Toolauth/wing-combo/docs/img/map/location-5v-power.png

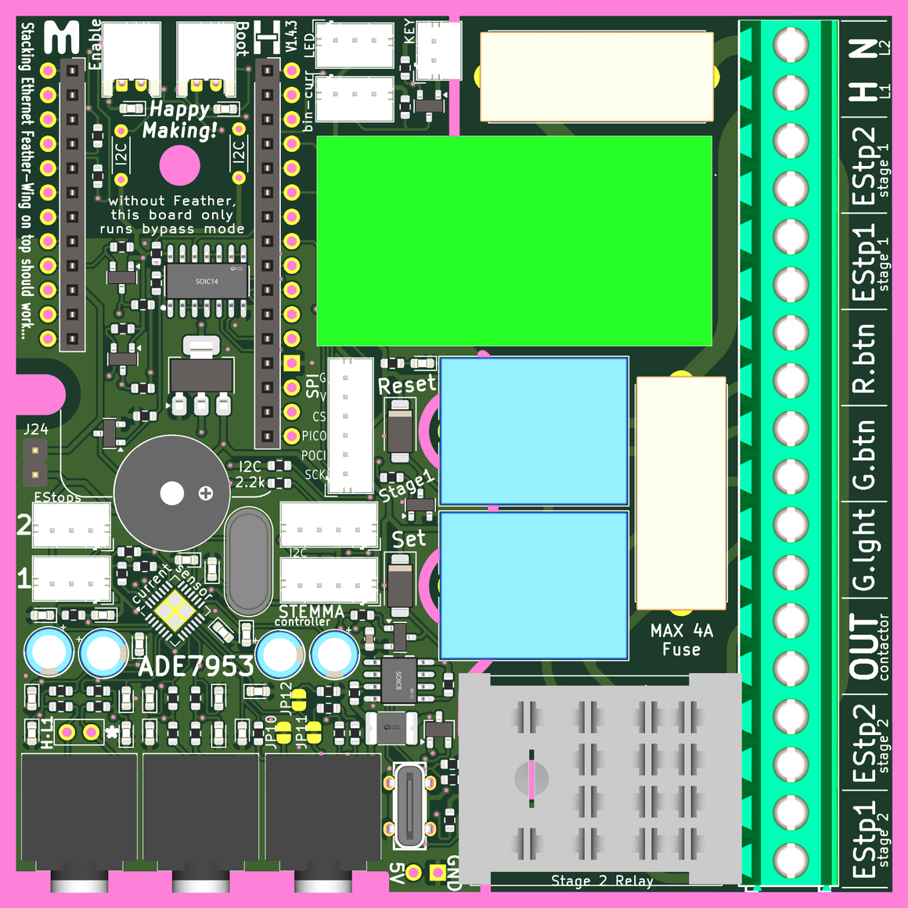
docs/img/map/location-5v-power.png
