Toolauth/wing-combo/docs/img/map/location-contactor.png

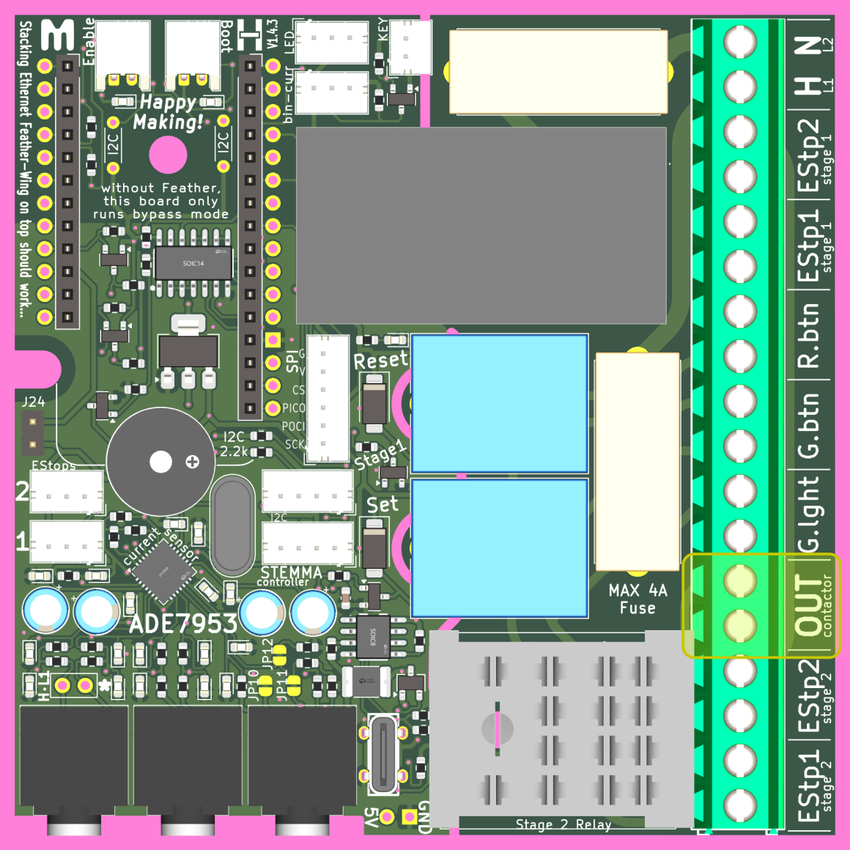
docs/img/map/location-contactor.png
