Toolauth/wing-combo/docs/img/map/location-current-a.png

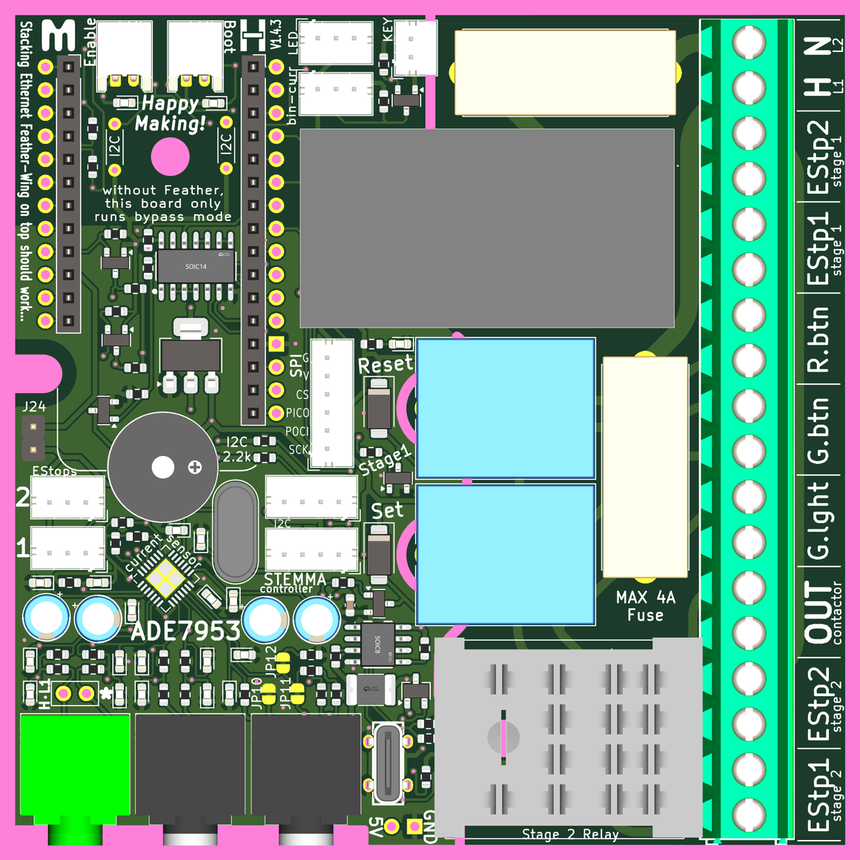
docs/img/map/location-current-a.png
