Toolauth/wing-combo/docs/img/map/location-current-b.png

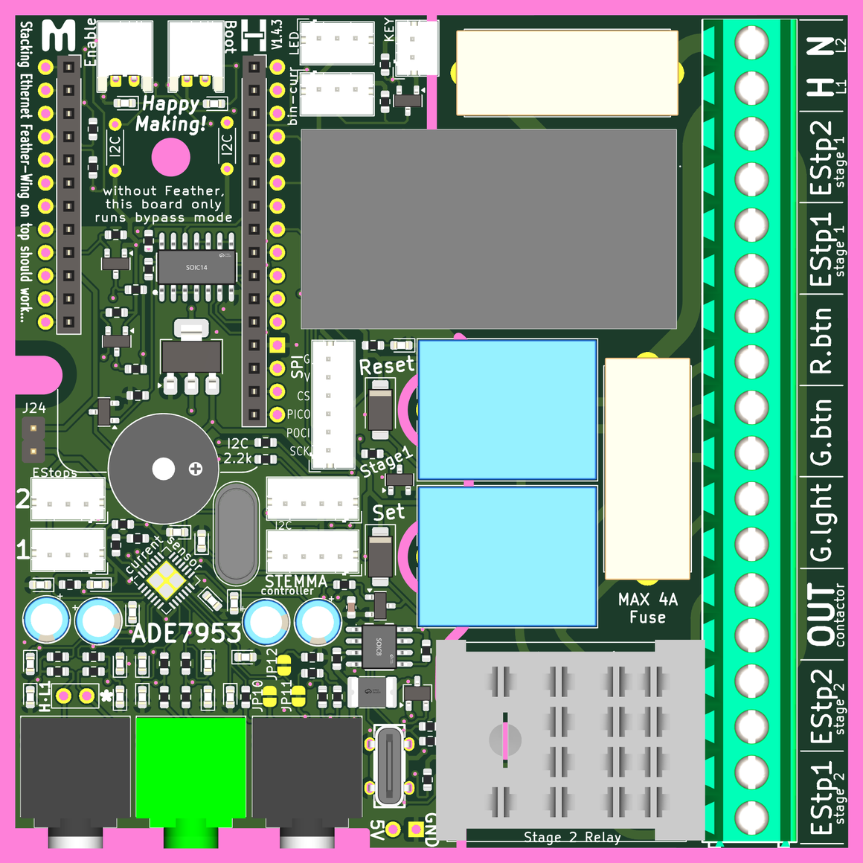
docs/img/map/location-current-b.png
