Toolauth/wing-combo/docs/img/map/location-feather-seat.png

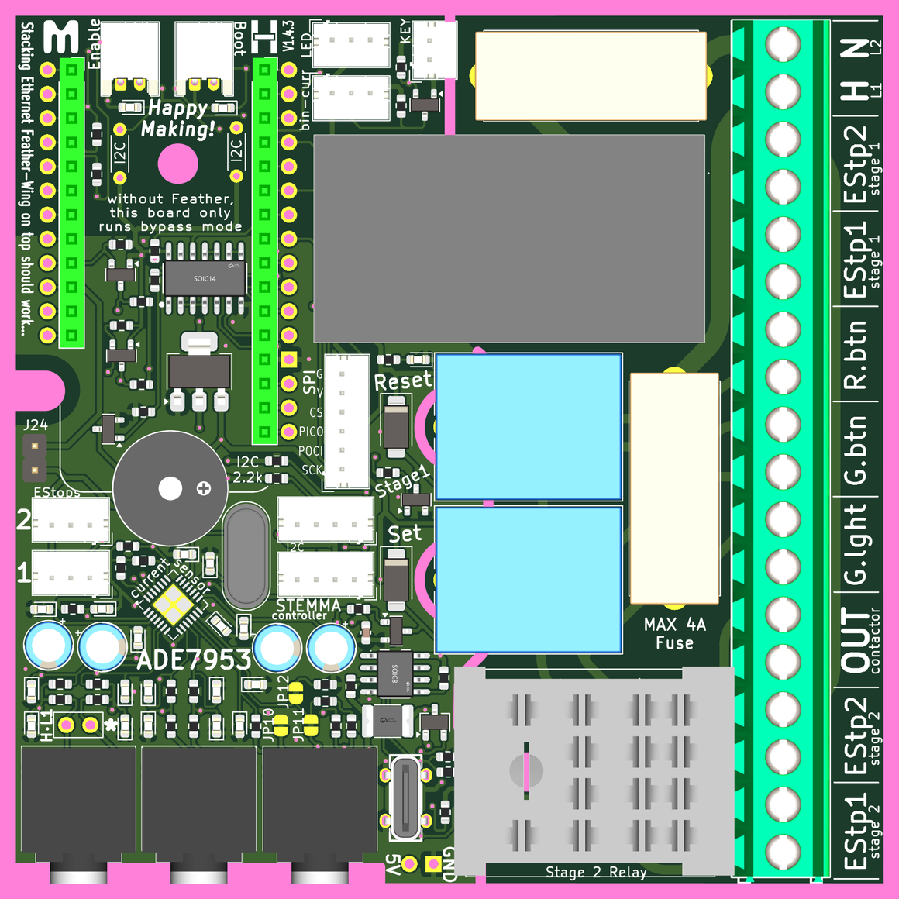
docs/img/map/location-feather-seat.png
