Toolauth/wing-combo/docs/img/map/location-fuses.png

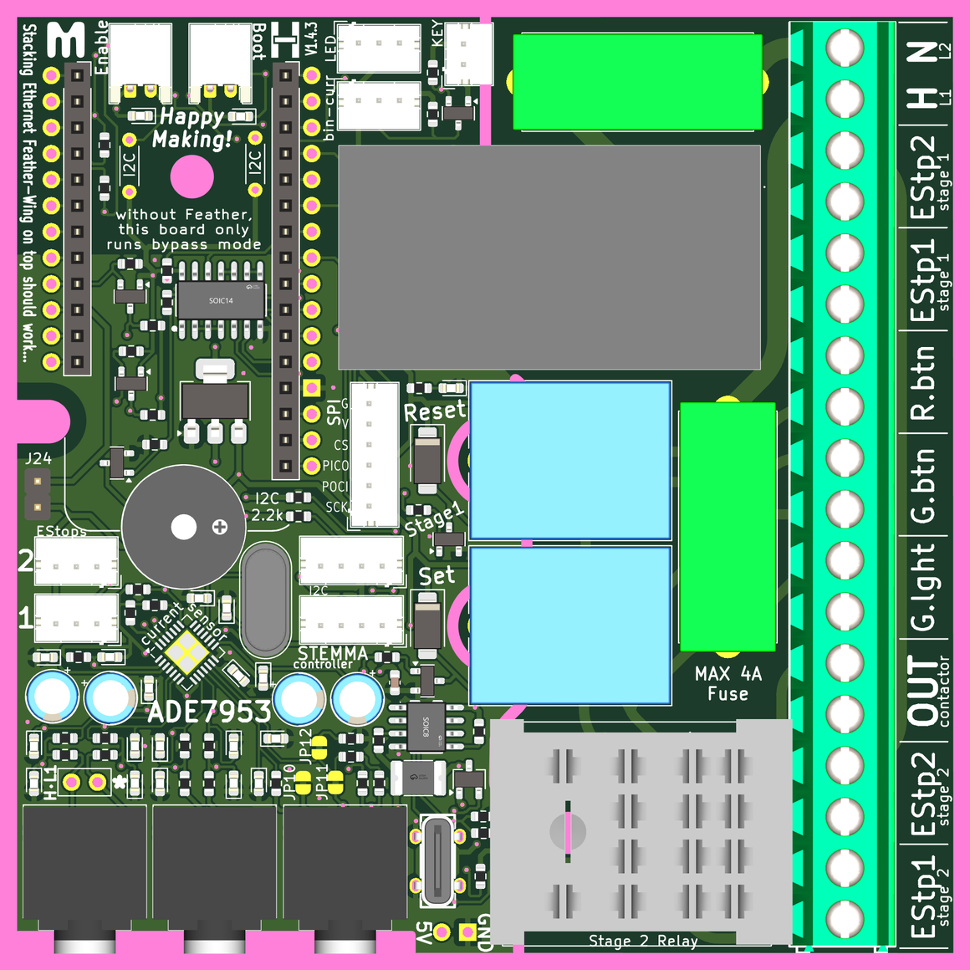
docs/img/map/location-fuses.png
