Toolauth/wing-combo/docs/img/map/location-i2c.png

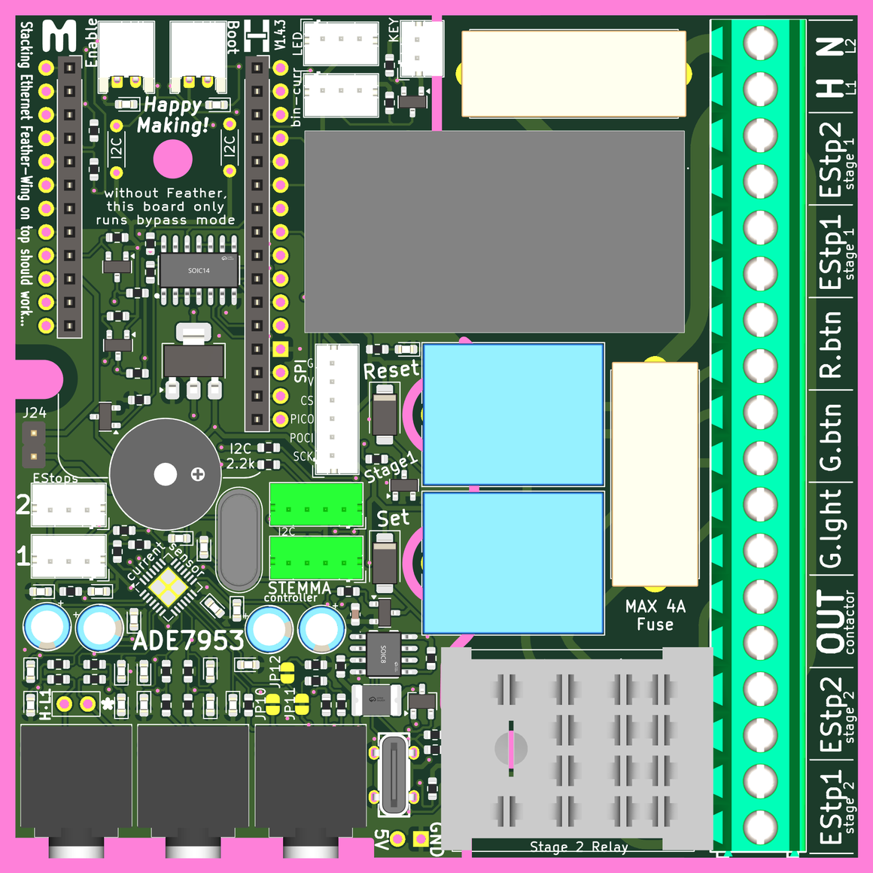
docs/img/map/location-i2c.png
