Toolauth/wing-combo/docs/img/map/location-stage-2.png

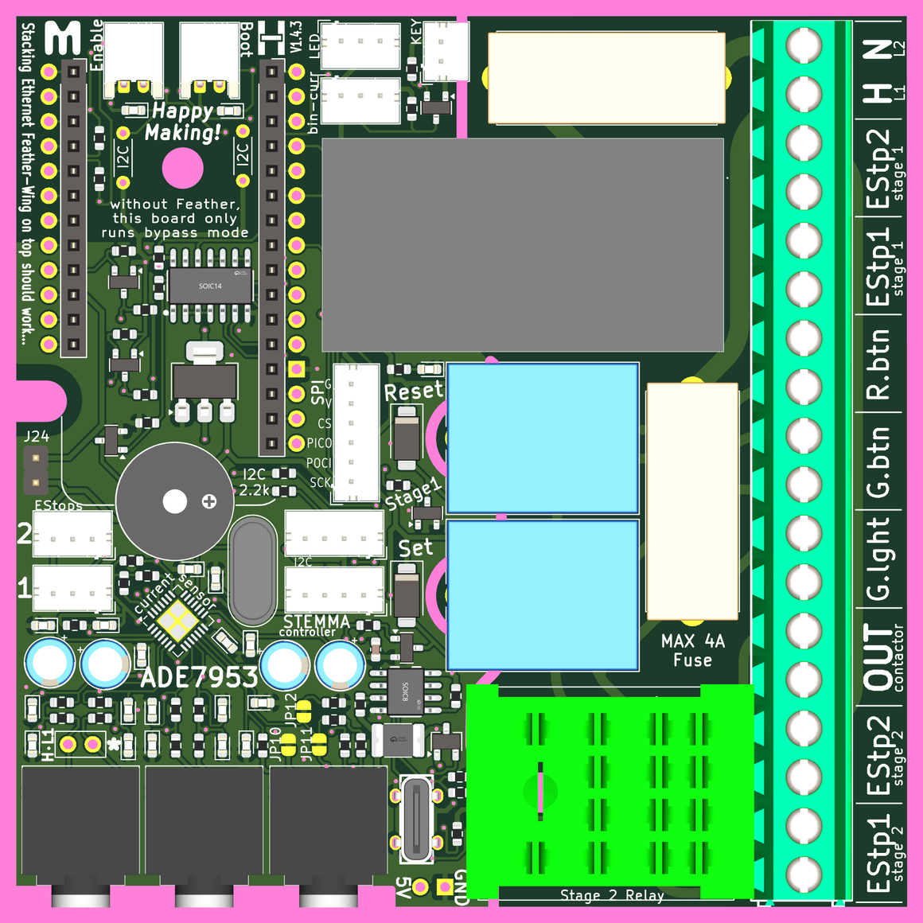
docs/img/map/location-stage-2.png
