Toolauth/wing-combo/docs/img/map/ortho-back-rt.png

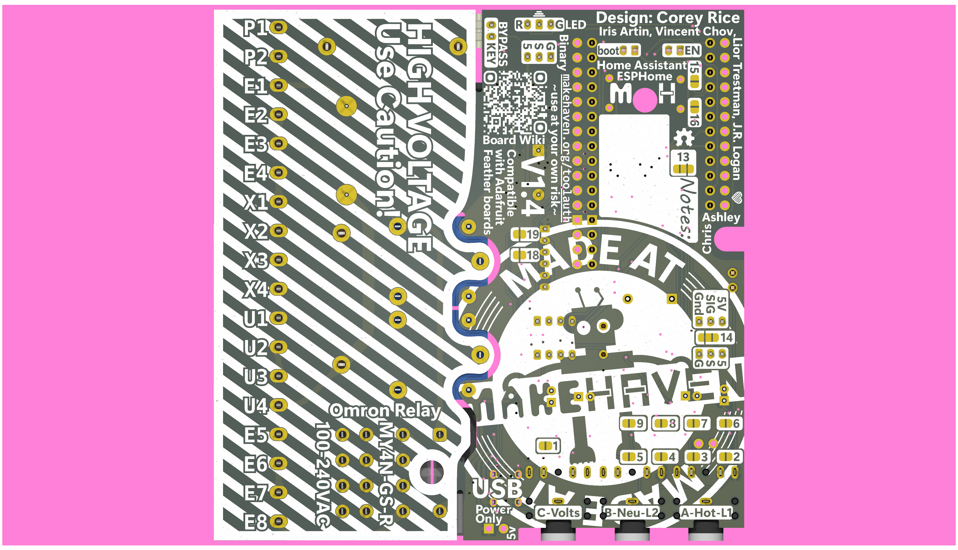
docs/img/map/ortho-back-rt.png
