Toolauth/wing-combo/docs/img/map/ortho-back.png

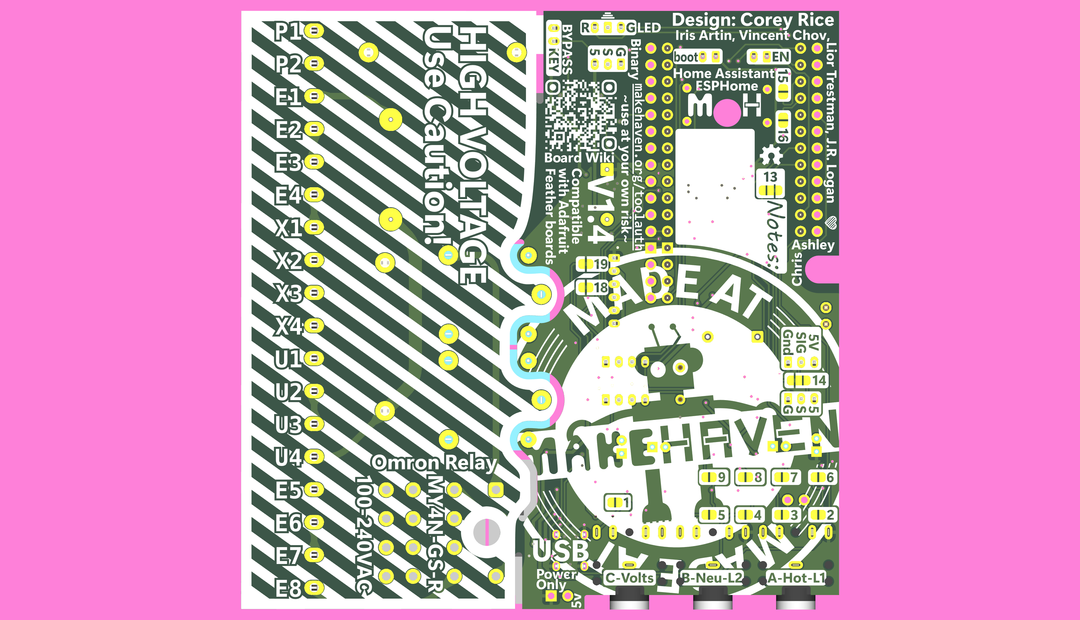
docs/img/map/ortho-back.png
