Toolauth/wing-combo/docs/img/map/ortho-front-rt.png

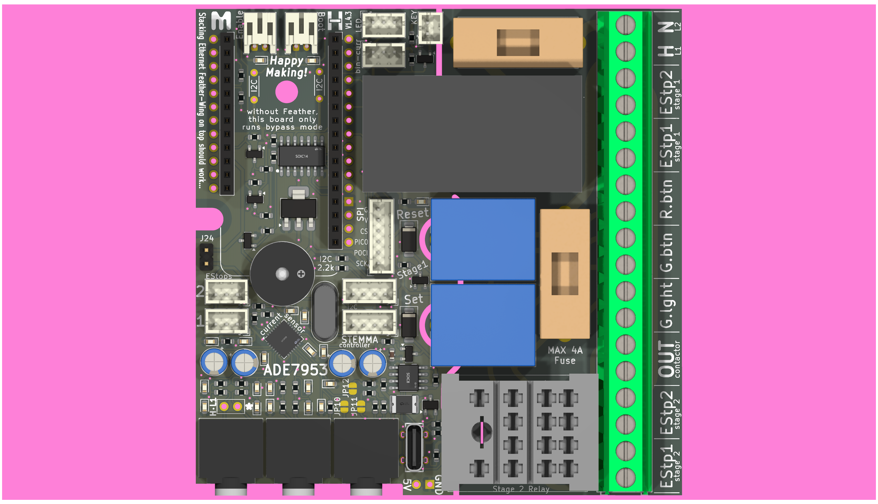
docs/img/map/ortho-front-rt.png
