Toolauth/wing-combo/docs/img/map/ortho-front.png

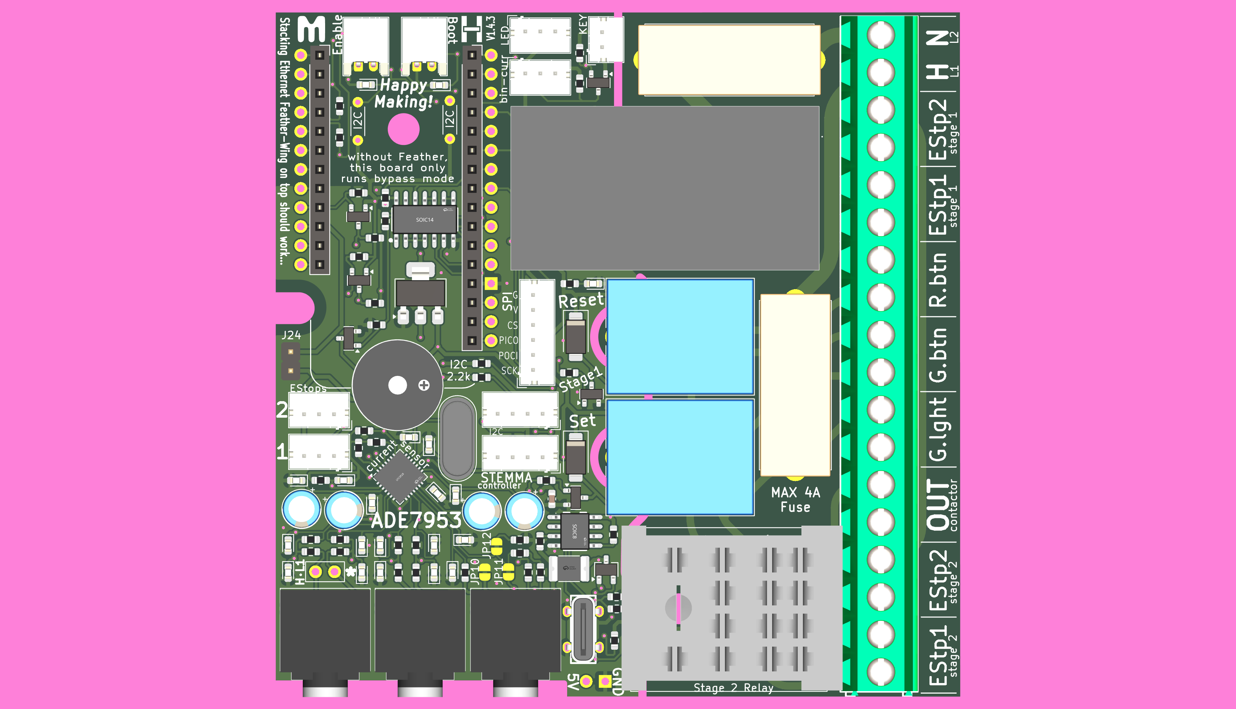
docs/img/map/ortho-front.png
