Toolauth/wing-combo/docs/img/map/sq-ortho-back.png

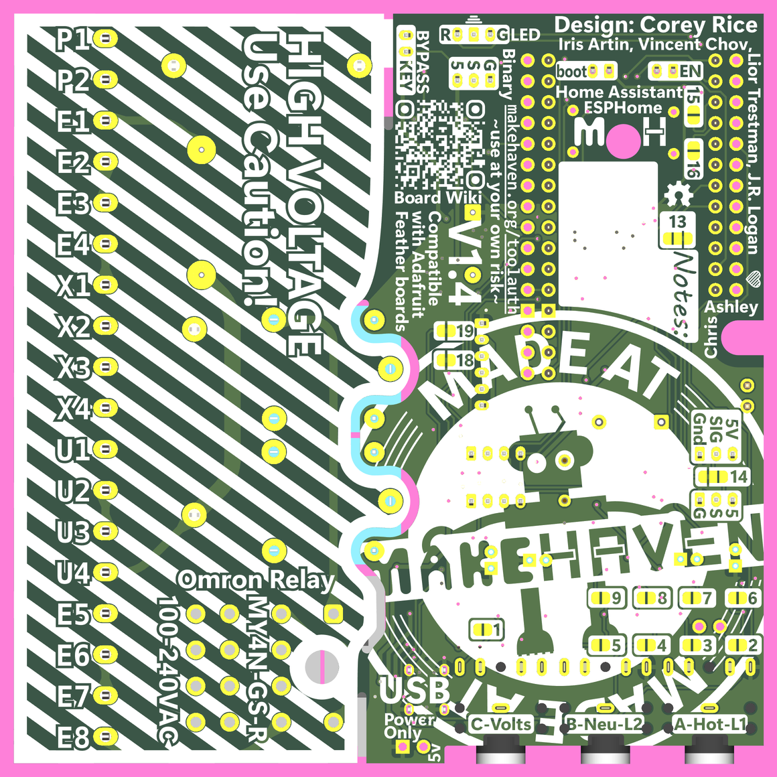
docs/img/map/sq-ortho-back.png
