Toolauth/wing-combo/docs/img/map/sq-ortho-front-rt.png

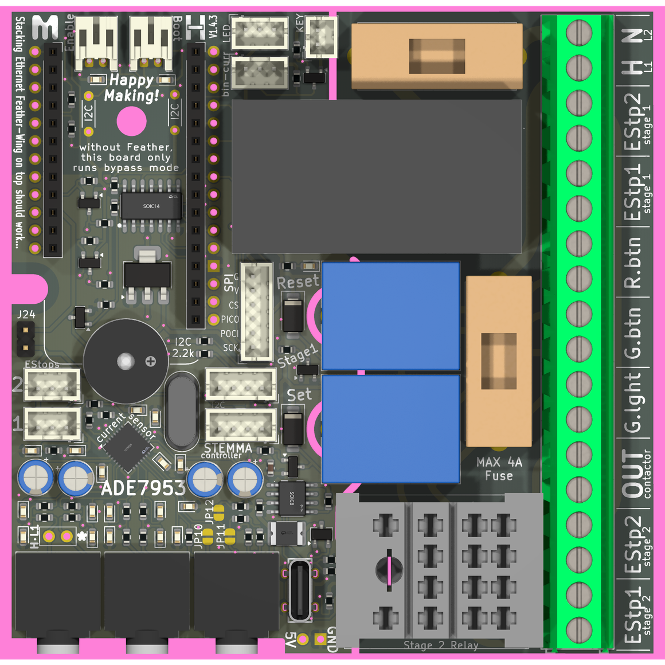
docs/img/map/sq-ortho-front-rt.png
