Toolauth/wing-combo/docs/img/offset-rt-front.png

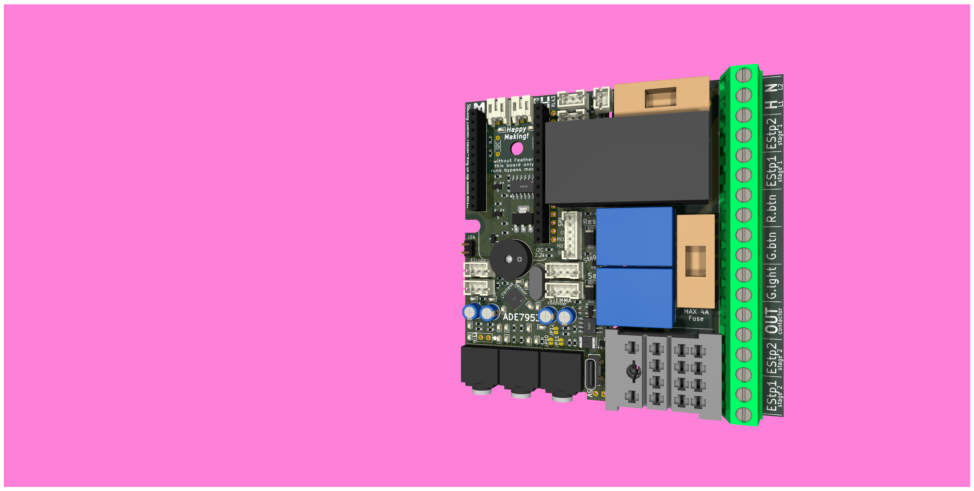
docs/img/offset-rt-front.png
