Toolauth/wing-combo/geometry/arduino_adafruit_products_fabprint.png

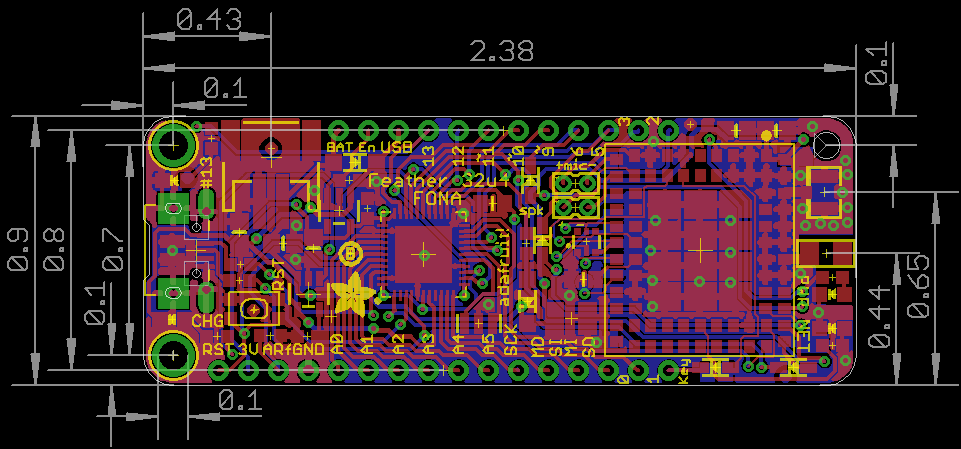
geometry/arduino_adafruit_products_fabprint.png
