Toolauth/wing-combo/docs/img/parts/one-estop-hookup.png

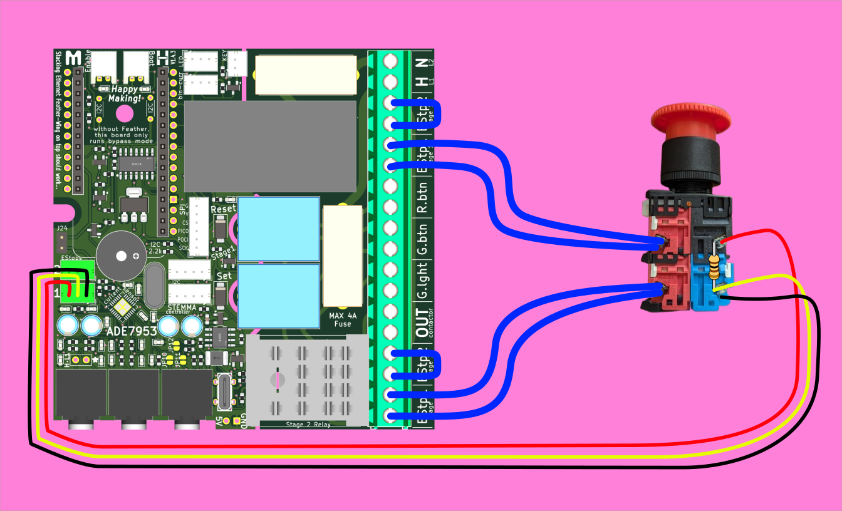
docs/img/parts/one-estop-hookup.png
